akih-san/EMUZ80-PICO-PICO2-adapter-card-for-MEZ65C_RAM/photo/PICO_PICO2_adapter_for_MEZ65C_RAM.png

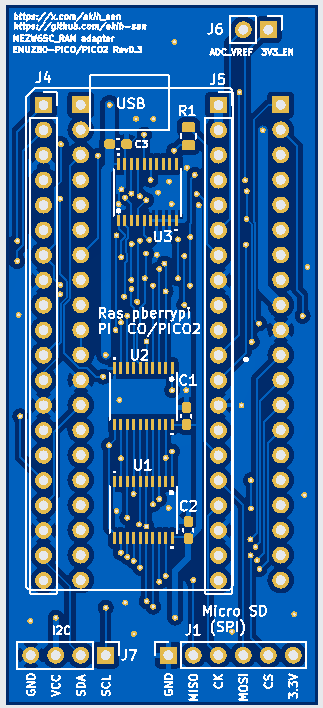
photo/PICO_PICO2_adapter_for_MEZ65C_RAM.png
